EdwardChamberlain/bambutton/tests/test_config_loader.py

import json
import re

from micro import config_loader


def test_web_setup_default_hostname_has_four_character_suffix():
    assert re.fullmatch(r"bambutton-[A-Z0-9]{4}", config_loader.DEFAULT_HOSTNAME)


def test_partial_config_keeps_explicit_settings_and_fills_defaults(tmp_path):
    config_path = tmp_path / "config.json"
    config_path.write_text(json.dumps({"wifi": {"hostname": "shop-button"}}))

    config = config_loader.load_config(config_path)

    assert config["wifi"]["hostname"] == "shop-button"
    assert config["wifi"]["ssid"] == ""
    assert config["api"]["base_url"] == ""
    assert config["printer"]["id"] is None
    assert not config_loader.is_runtime_config_ready(config)


def test_malformed_config_recovers_from_valid_backup(tmp_path):
    config_path = tmp_path / "config.json"
    backup_path = tmp_path / "config.json.bak"
    config_path.write_text('{"wifi":')
    backup_path.write_text(json.dumps({
        "wifi": {"ssid": "shop"},
        "api": {"base_url": "http://bambuddy/api/v1"},
        "printer": {"id": 7},
    }))

    config = config_loader.load_config(config_path)

    assert config["wifi"]["ssid"] == "shop"
    assert config["printer"]["id"] == 7


def test_malformed_config_without_backup_uses_bootable_defaults(tmp_path):
    config_path = tmp_path / "config.json"
    config_path.write_text('{"wifi":')

    config = config_loader.load_config(config_path)

    assert config["wifi"]["ssid"] == ""
    assert config["api"]["base_url"] == ""
    assert config["printer"]["id"] is None
    assert config["web"]["password"]
    assert not config_loader.is_runtime_config_ready(config)


def test_nested_invalid_active_config_recovers_from_valid_backup(tmp_path):
    config_path = tmp_path / "config.json"
    backup_path = tmp_path / "config.json.bak"
    config_path.write_text(json.dumps({"wifi": None}))
    backup_path.write_text(json.dumps({
        "wifi": {"ssid": "shop"},
        "api": {"base_url": "http://bambuddy/api/v1", "key": "secret"},
        "printer": {"id": 7},
    }))

    config = config_loader.load_config(config_path)

    assert config["wifi"]["ssid"] == "shop"
    assert config["printer"]["id"] == 7
    assert config_loader.is_runtime_config_ready(config)


def test_incomplete_config_never_inherits_a_printer_id(tmp_path):
    config_path = tmp_path / "config.json"
    config_path.write_text(json.dumps({
        "wifi": {"ssid": "shop"},
        "api": {"base_url": "http://bambuddy/api/v1", "key": "secret"},
    }))

    config = config_loader.load_config(config_path)

    assert config["printer"]["id"] is None
    assert not config_loader.is_runtime_config_ready(config)


def test_non_numeric_printer_id_is_rejected_and_uses_safe_defaults(tmp_path):
    config_path = tmp_path / "config.json"
    config_path.write_text(json.dumps({"printer": {"id": "3"}}))

    config = config_loader.load_config(config_path)

    assert config["printer"]["id"] is None
    assert not config_loader.is_runtime_config_ready(config)
